pfliegster/trinket-m0-enclosure/images/enclosure_bottom_with_pwb.png

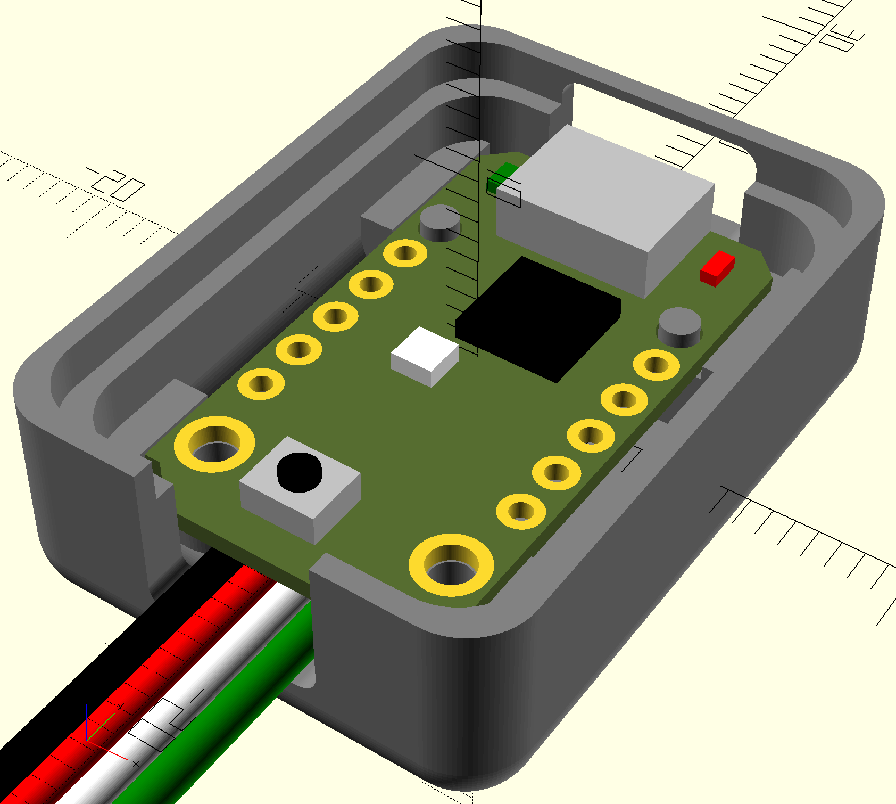
images/enclosure_bottom_with_pwb.png
